devtank-ltd/osm_kicard_v2/kicad_osm_env01/OSM_env01__revB_img4.png

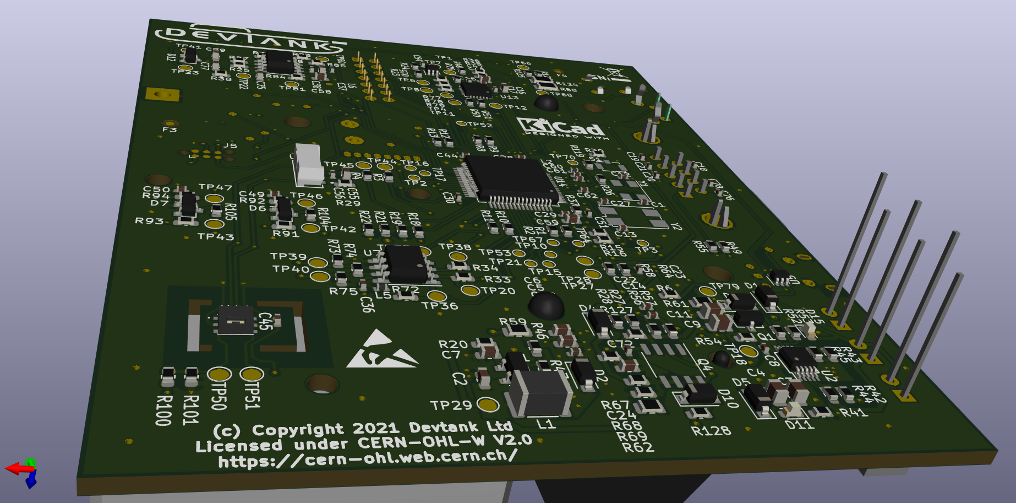
kicad_osm_env01/OSM_env01__revB_img4.png
