devtank-ltd/osm_kicard_v2/kicad_osm_env01/OSM_env03.png

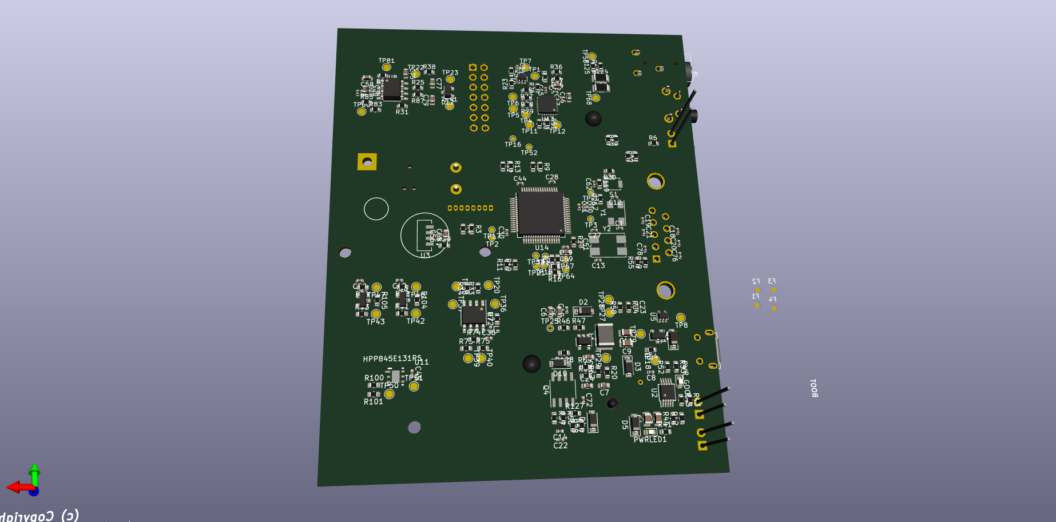
kicad_osm_env01/OSM_env03.png
